FPGA-Computer/Timer/V2/firmware/time.c

/*
 * time.c
 *
 * Created: October-23-18, 10:12:33 PM
 *  Author: K. C. Lee
 * Copyright (c) 2017 by K. C. Lee
 
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
 If not, see http://www.gnu.org/licenses/gpl-3.0.en.html 
 */ 
#include "hardware.h"

volatile rtc_t time;
volatile prefs_t Prefs;
uint8_t tim1_tick = TICK_MAX-1;

uint32_t DDS_PhaseInc;
volatile uint32_t DDS_Accum;

void Time_Init(void)
{	// prescaler
	TIM1->PSCRH = (TIM1_PRESCALER-1) >> 8;
	TIM1->PSCRL = (TIM1_PRESCALER-1) & 0xff;
	// Autoreload
	TIM1->ARRH = (TIM1_RELOAD-1) >> 8;
	TIM1->ARRL = (TIM1_RELOAD-1) & 0xff;	

	// Preload, Counter enable
	TIM1->CR1 = TIM1_CR1_ARPE|TIM1_CR1_CEN;
	// Update Interrupt
	TIM1->IER = TIM1_IER_UIE;

	#ifdef DST
		time.DST_Enable = Prefs.TimeOpt;
	#endif
	
	// use DDS for clock fine adjustments
	RTC_SetNCO(Prefs.DDS_Adj);
	RTC_SetDate(1,1,YEAR_START);
}

// RTC

@far @interrupt void TIM1_IRQ(void)
{	
	// clear UIF
	TIM1->SR1 &= ~TIM1_SR1_UIF;
	time.Tick = 1;
	
	if(tim1_tick)
	{
		tim1_tick--;
		return;
	}
	
	tim1_tick = TICK_MAX-1;

	// RTC timebase comes from Direct Digital Synthesis
	DDS_Accum += DDS_PhaseInc;

	if (DDS_Accum & DDS_CARRY)
	{
		DDS_Accum &= DDS_MASK;
	
		if(time.ticks)
		{	
			// blink decimal point
			if(time.ticks==(TICKS_PER_SEC/2))
				time.HalfSec = 1;
	
			time.ticks--;
		}
		else
		{
			time.ticks = TICKS_PER_SEC-1;
	
			time.sec++;
			
			if(time.sec > 59)
			{
				time.sec = 0;
				time.min++;
			
				if(time.min > 59)
				{
					time.min = 0;			
					time.hour++;
					
					#ifdef DST
						if(time.DST_Enable)	// check every hour on the hour
							DST_Check();
					#endif	
				}
				if(time.hour > TIME_HR_MAX)
				{
					time.hour = TIME_HR_MIN;
					
					if(time.dayofweek < 6)
						time.dayofweek++;
					else
						time.dayofweek = 0;
					
					if(time.day<MonthDays(time.month,time.year))
						time.day++;
					else
					{
						time.day = 1;
						
						if(time.month <12)
							time.month++;
						else
						{
							time.month = 1;
							time.year++;
							RTC_AnnualUpdate();
						}
					}
				}

				// Servo on/off
				if(power&&(Prefs.al_hour == time.hour)&&(Prefs.al_min == time.min))
				{
					time.al_length1 = Prefs.al_length1;
					time.al_length2 = Prefs.al_length2;			
					MOTOR_ON();
				}
			}
			
			if(power)
			{
				if(time.al_length1)
				{
					if(time.al_length1==1)
						MOTOR_OFF();
						
					time.al_length1--;
				}
				
				if(time.al_length2)
				{
					if(time.al_length2==1)
						LED_OFF();
					else
					{
						// LED on/off
						if(ADC_Result>Prefs.adc_threshold+ADC_HYSTERESIS)
							LED_ON();
						else if(ADC_Result<Prefs.adc_threshold)
							LED_OFF();				
					}
					time.al_length2--;
				}
		
				time.SecFlag = 1;
				time.FullSec = 1;
			}
		}	
	}
}

/* https://www.wikihow.com/Calculate-Leap-Years */
uint8_t LeapYear(uint8_t year)
{
	if(year%4)
		return(0);
	else if(year%100)
		return(1);
	else if(year%400)
		return(0);
	else			
		return(1);
}

void RTC_AnnualUpdate(void)
{
	time.LeapYear=LeapYear(time.year);

	#ifdef DST
		if(time.DST_Enable)
		{
			uint8_t dayofweek;

			dayofweek = DayWeek(1,DST_Start_Month,time.year);
			time.DST_Start = 1+ 7*(dayofweek?DST_Start_Week:DST_Start_Week-1) - dayofweek;
			dayofweek = DayWeek(1,DST_End_Month,time.year);
			time.DST_Stop = 1+ 7*(dayofweek?DST_End_Week:DST_End_Week-1) - dayofweek;
		}
	#endif		
}

// months starts at 1
const uint8_t MonthDays_Tbl[]= { 0,31,28,31,30,31,30,31,31,30,31,30,31 };

uint8_t MonthDays(uint8_t month, uint16_t year)
{
	if((month !=2)||!time.LeapYear)
	  return(MonthDays_Tbl[month]);
	else
		return(29);
}

/*
	https://en.wikipedia.org/wiki/Determination_of_the_day_of_the_week
	Sakamoto's methods
*/
uint8_t DayWeek(uint8_t Day, uint8_t Month, uint16_t Year)
{
	const uint8_t t[] = {0, 3, 2, 5, 0, 3, 5, 1, 4, 6, 2, 4};
	uint16_t y;

	y = Year - (Month < 3);
	return ((y + y/4 - y/100 + y/400 + t[Month-1] + Day) % 7);
}

#ifdef DST

void DST_Check(void)
{
	if(time.DST_Active)
	{
		if(	(time.month == DST_End_Month)&&
				(time.day == time.DST_Stop)&&
				(time.hour == DST_ChangeTime) )
		{
			time.hour --;
			time.DST_Active = 0;
		}
	}
	else
	{
		if(	(time.month == DST_Start_Month)&&
				(time.day == time.DST_Start)&&
				(time.hour == DST_ChangeTime) )
		{
			time.hour ++;
			time.DST_Active = 1;
		}
	}
}

// Quick & dirty date compare - ignore differences in # of days in the month
int16_t DST_CmpDates(uint8_t M,uint8_t D)
{
	return((time.month-M)*31+(time.day-D));
}

int32_t DST_CmpTime(void)
{
	return((time.hour-DST_ChangeTime)*3600UL + time.min*60UL + time.sec);
}

// fix up DST state after time/data change
void DST_FixState(void)
{	int16_t cmp;

	cmp=DST_CmpDates(DST_Start_Month,time.DST_Start);

	if(cmp<0)								// < DST start date
		time.DST_Active = 0;
	else if(cmp==0)					// == DST start date
		time.DST_Active = (DST_CmpTime()>=0);
	else										// > DST start date
	{
		cmp=DST_CmpDates(DST_End_Month,time.DST_Stop);	
		
		if(cmp<0)							// < DST end date
			time.DST_Active = 1;
		else if(cmp==0)				// == DST end date
			time.DST_Active = (DST_CmpTime()< 0L);
		else									// > DST end date
			time.DST_Active = 0;
	}
}
#endif		

void RTC_SetNCO(int16_t Adj)
{
	// use DDS for clock fine adjustments
	DDS_PhaseInc = DDS_INC + Adj;
}

void RTC_SetTime(uint8_t Hour, uint8_t Min, uint8_t Sec)
{
	sim();
	time.hour =	Hour;
	time.min =	Min;	
	time.sec =	Sec;
	time.ticks = TICKS_PER_SEC-1;
	
#ifdef DST	
	DST_FixState();
#endif
	AdjustAlarm();
	rim();
}

void RTC_SetDate(uint8_t Day, uint8_t Month, uint16_t Year)
{	
	uint8_t dayofweek;

	dayofweek=DayWeek(Day,Month,Year);
	sim();
	time.dayofweek = dayofweek;
	time.day = Day;
	time.month = Month;	
	time.year =	Year;
	RTC_AnnualUpdate();
	DST_FixState();
	rim();
}

void AdjustAlarm(void)
{
	uint32_t Current_Time, Alarm_Time;
	
	// time in seconds 
	Current_Time = (time.hour * 60UL +  time.min)*60UL + time.sec;
	Alarm_Time = (Prefs.al_hour * 60UL + Prefs.al_min)*60UL;
	
	if(Current_Time < Alarm_Time)
	{
		time.al_length1 = 0;
		time.al_length2 = 0;		
	}
	else		// calculate remaining alarm time
	{
		Alarm_Time = Current_Time - Alarm_Time;
		
		if(Prefs.al_length1 > Alarm_Time)
			time.al_length1 = Prefs.al_length1 - Alarm_Time;
		else
			time.al_length1 = 0;
	
		if(Prefs.al_length2 > Alarm_Time)
			time.al_length2 = Prefs.al_length2 - Alarm_Time;
		else
			time.al_length2 = 0;	
	}
	
	if(time.al_length1)
		MOTOR_ON();
	else
		MOTOR_OFF();	
}
