FPGA-Computer/Timer/V2/firmware/LCD.c

/*
 * lcd.c
 *
 * Created: April-08-15, 3:09:59 PM
 *  Author: K. C. Lee
 * Copyright (c) 2017 by K. C. Lee
 
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
 If not, see http://www.gnu.org/licenses/gpl-3.0.en.html 
 */ 
#include "LCD.h"

// minimum delay for 12MHz
uint8_t LCD_X, LCD_Y, LCD_CharSet;

#define LCD_Short_Delay() _asm("nop")

void LCD_WR_High_Nibble(uint8_t Code)
{  
	LCD_DATA_PORT->ODR = Code;
	LCD_Short_Delay();
	LCD_E_PORT->ODR |= LCD_E;
	LCD_Short_Delay();	
	LCD_E_PORT->ODR &= ~LCD_E;
}

void LCD_WR(uint8_t LCD_data)
{ 
	// DDR, RS = Output
	LCD_DATA_PORT->CR1=LCD_DATA_PORT->DDR |= LCD_DATA;
	LCD_RS_PORT->DDR |= LCD_RS;
	
  LCD_WR_High_Nibble(LCD_data & 0xf0);
  LCD_WR_High_Nibble(LCD_data << 4);
	
  // Data, RS = Input  
  LCD_DATA_PORT->CR1 = LCD_DATA_PORT->DDR &= ~LCD_DATA;	
	LCD_RS_PORT->DDR &= ~LCD_RS;
	LCD_Short_Delay();
 }

void LCD_Wait(void)
{
	Delay(_LCD_DELAY_CHAR);
}

void LCD_Data(uint8_t LCD_Data)
{ 
  LCD_RS_PORT->ODR = LCD_RS;
  LCD_WR(LCD_Data);
  LCD_Wait();
 }

void LCD_Cmd(uint8_t Cmd)
{ 
  LCD_RS_PORT->ODR = 0;
  LCD_WR(Cmd);
  LCD_Wait();
 }

// Cursor support
void LCD_Moveto(uint8_t X, uint8_t Y)
{ 
	LCD_X = X & _LCD_XMASK;
	LCD_Y = Y & _LCD_YMASK;
	
	LCD_Cmd(_LCD_DD|LCD_Addr(LCD_X,LCD_Y));
 }

void LCD_Ch(uint8_t Ch)
{
	LCD_Data(Ch);
	LCD_X++;
	
	if(LCD_X > _LCD_XMASK)
	{
		LCD_X = 0;
		LCD_Y = 1;
		
		LCD_Moveto(0,1);
	}
 }

LCD_CUSTOM_CHR
const uint8_t LCD_CG[]=
{ 
	0x0e,0x11,0x1f,0x11,0x00,0x11,0x1b,0x15,		// AM
	0x1e,0x11,0x1e,0x10,0x00,0x11,0x1b,0x15,		// PM
	0x04,0x0e,0x1f,0x00,0x1f,0x0e,0x04,0x00,		// Adj
	0x08,0x05,0x03,0x17,0x08,0x05,0x03,0x07,		// Light
};

void LCD_UserCh(void)
{ uint8_t i;

  LCD_Cmd(_LCD_CG);
  
  for(i=0;i<sizeof(LCD_CG);i++)
    LCD_Data(LCD_CG[i]);

  LCD_Cmd(_LCD_DD);  
 }

void LCD_Puts(char *str)
{
	while(*str)
	  LCD_Ch(*str++);
}

void LCD_Cls(void)
{
	LCD_Cmd(_LCD_CLR);
	Delay(_LCD_DELAY_CLR);
	LCD_X = LCD_Y = 0;
}

// Power On LCD reset    
void LCD_Init(void)
{ 
	// GPIO for LCD
	LCD_E_PORT->DDR = LCD_E|LCD_DATA;
	// Fast push-pull
	LCD_E_PORT->CR1 = LCD_E_PORT->CR2 = LCD_E;
	// DDR, RS = Output
	LCD_RS_PORT->DDR = LCD_RS_PORT->CR1 = LCD_RS;

	LCD_WR_High_Nibble(_LCD_Set8bit);
	Delay(_LCD_INIT_DELAY1);
	
	LCD_WR_High_Nibble(_LCD_Set8bit);
	Delay(_LCD_INIT_DELAY2);
	
	LCD_WR_High_Nibble(_LCD_Set8bit);	
	LCD_WR_High_Nibble(_LCD_FuncSetH);
	
	Delay(_LCD_DELAY_CHAR);							// Set8bit: 39us
	LCD_Cmd(_LCD_FuncSet);

	LCD_Cls();	
	LCD_Cmd(_LCD_ON|_LCD_DISPLAY_ON);	
	LCD_UserCh();
	LCD_Cmd(_LCD_ENTRY);
 }

void LCD_Off(void)
{
	// Set LCD GPIO = '0' to prevent leakages
	LCD_E_PORT->ODR = 0;
	LCD_RS_PORT->ODR = 0;
	LCD_RS_PORT->DDR = LCD_RS;
}
